patrickleboutillier/flash6502/docs/kicad/flash6502/ALU.kicad_sch

## KiCad design docs/kicad/flash6502/ALU.kicad_sch (2023-03-12, an earlier design)

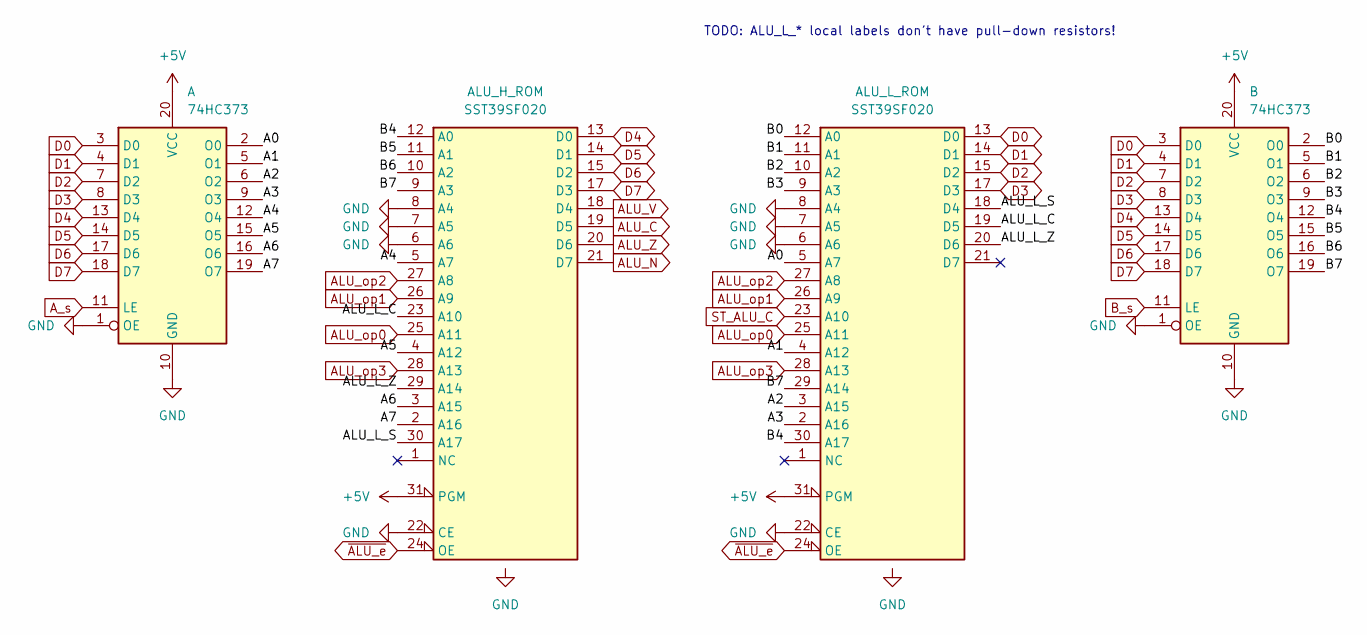
[picture p24: schematic ALU.kicad_sch]

Parts:
A: 74HC373
ALU_H_ROM: SST39SF020
ALU_L_ROM: SST39SF020
B: 74HC373

Connections:
+5V: A.20 (VCC), ALU_H_ROM.31 (PGM), ALU_L_ROM.31 (PGM), B.20 (VCC)
A0: A.2 (O0), ALU_L_ROM.5 (A7)
A1: A.5 (O1), ALU_L_ROM.4 (A12)
A2: A.6 (O2), ALU_L_ROM.3 (A15)
A3: A.9 (O3), ALU_L_ROM.2 (A16)
A4: A.12 (O4), ALU_H_ROM.5 (A7)
A5: A.15 (O5), ALU_H_ROM.4 (A12)
A6: A.16 (O6), ALU_H_ROM.3 (A15)
A7: A.19 (O7), ALU_H_ROM.2 (A16)
ALU_C: ALU_H_ROM.19 (D5)
ALU_L_C: ALU_H_ROM.23 (A10), ALU_L_ROM.19 (D5)
ALU_L_S: ALU_H_ROM.30 (A17), ALU_L_ROM.18 (D4)
ALU_L_Z: ALU_H_ROM.29 (A14), ALU_L_ROM.20 (D6)
ALU_N: ALU_H_ROM.21 (D7)
ALU_V: ALU_H_ROM.18 (D4)
ALU_Z: ALU_H_ROM.20 (D6)
ALU_op0: ALU_H_ROM.25 (A11), ALU_L_ROM.25 (A11)
ALU_op1: ALU_H_ROM.26 (A9), ALU_L_ROM.26 (A9)
ALU_op2: ALU_H_ROM.27 (A8), ALU_L_ROM.27 (A8)
ALU_op3: ALU_H_ROM.28 (A13), ALU_L_ROM.28 (A13)
A_s: A.11 (LE)
B0: ALU_L_ROM.12 (A0), B.2 (O0)
B1: ALU_L_ROM.11 (A1), B.5 (O1)
B2: ALU_L_ROM.10 (A2), B.6 (O2)
B3: ALU_L_ROM.9 (A3), B.9 (O3)
B4: ALU_H_ROM.12 (A0), ALU_L_ROM.30 (A17), B.12 (O4)
B5: ALU_H_ROM.11 (A1), B.15 (O5)
B6: ALU_H_ROM.10 (A2), B.16 (O6)
B7: ALU_H_ROM.9 (A3), ALU_L_ROM.29 (A14), B.19 (O7)
B_s: B.11 (LE)
D0: A.3 (D0), ALU_L_ROM.13 (D0), B.3 (D0)
D1: A.4 (D1), ALU_L_ROM.14 (D1), B.4 (D1)
D2: A.7 (D2), ALU_L_ROM.15 (D2), B.7 (D2)
D3: A.8 (D3), ALU_L_ROM.17 (D3), B.8 (D3)
D4: A.13 (D4), ALU_H_ROM.13 (D0), B.13 (D4)
D5: A.14 (D5), ALU_H_ROM.14 (D1), B.14 (D5)
D6: A.17 (D6), ALU_H_ROM.15 (D2), B.17 (D6)
D7: A.18 (D7), ALU_H_ROM.17 (D3), B.18 (D7)
GND: A.1 (OE), A.10 (GND), ALU_H_ROM.6 (A6), ALU_H_ROM.7 (A5), ALU_H_ROM.8 (A4), ALU_H_ROM.16 (GND), ALU_H_ROM.22 (CE), ALU_L_ROM.6 (A6), ALU_L_ROM.7 (A5), ALU_L_ROM.8 (A4), ALU_L_ROM.16 (GND), ALU_L_ROM.22 (CE), B.1 (OE), B.10 (GND)
ST_ALU_C: ALU_L_ROM.23 (A10)
~ALU_e: ALU_H_ROM.24 (OE), ALU_L_ROM.24 (OE)

Notes on the sheet:
TODO: ALU_L_* local labels don't have pull-down resistors!
