patrickleboutillier/flash6502/docs/kicad/flash6502/Address_High.kicad_sch

## KiCad design docs/kicad/flash6502/Address_High.kicad_sch (2023-03-12, an earlier design)

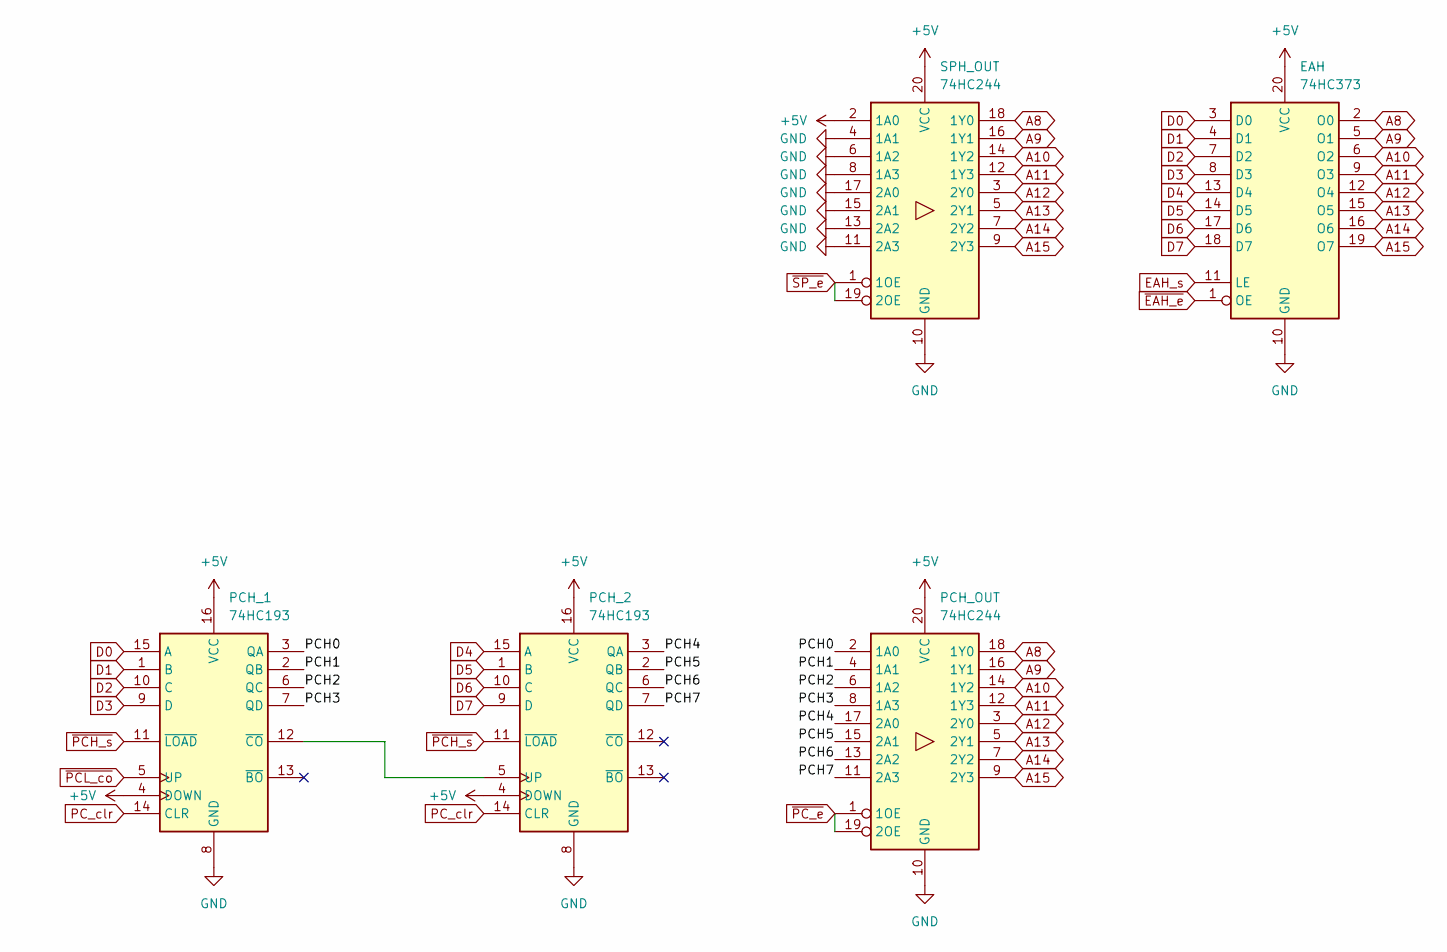
[picture p25: schematic Address_High.kicad_sch]

Parts:
EAH: 74HC373
PCH_1, PCH_2: 74HC193
PCH_OUT: 74HC244
SPH_OUT: 74HC244

Connections:
+5V: EAH.20 (VCC), PCH_1.4 (DOWN), PCH_1.16 (VCC), PCH_2.4 (DOWN), PCH_2.16 (VCC), PCH_OUT.20 (VCC), SPH_OUT.2 (1A0), SPH_OUT.20 (VCC)
A8: EAH.2 (O0), PCH_OUT.18 (1Y0), SPH_OUT.18 (1Y0)
A9: EAH.5 (O1), PCH_OUT.16 (1Y1), SPH_OUT.16 (1Y1)
A10: EAH.6 (O2), PCH_OUT.14 (1Y2), SPH_OUT.14 (1Y2)
A11: EAH.9 (O3), PCH_OUT.12 (1Y3), SPH_OUT.12 (1Y3)
A12: EAH.12 (O4), PCH_OUT.3 (2Y0), SPH_OUT.3 (2Y0)
A13: EAH.15 (O5), PCH_OUT.5 (2Y1), SPH_OUT.5 (2Y1)
A14: EAH.16 (O6), PCH_OUT.7 (2Y2), SPH_OUT.7 (2Y2)
A15: EAH.19 (O7), PCH_OUT.9 (2Y3), SPH_OUT.9 (2Y3)
D0: EAH.3 (D0), PCH_1.15 (A)
D1: EAH.4 (D1), PCH_1.1 (B)
D2: EAH.7 (D2), PCH_1.10 (C)
D3: EAH.8 (D3), PCH_1.9 (D)
D4: EAH.13 (D4), PCH_2.15 (A)
D5: EAH.14 (D5), PCH_2.1 (B)
D6: EAH.17 (D6), PCH_2.10 (C)
D7: EAH.18 (D7), PCH_2.9 (D)
EAH_s: EAH.11 (LE)
GND: EAH.10 (GND), PCH_1.8 (GND), PCH_2.8 (GND), PCH_OUT.10 (GND), SPH_OUT.4 (1A1), SPH_OUT.6 (1A2), SPH_OUT.8 (1A3), SPH_OUT.10 (GND), SPH_OUT.11 (2A3), SPH_OUT.13 (2A2), SPH_OUT.15 (2A1), SPH_OUT.17 (2A0)
unnamed: PCH_1.12 (~CO), PCH_2.5 (UP)
PCH0: PCH_1.3 (QA), PCH_OUT.2 (1A0)
PCH1: PCH_1.2 (QB), PCH_OUT.4 (1A1)
PCH2: PCH_1.6 (QC), PCH_OUT.6 (1A2)
PCH3: PCH_1.7 (QD), PCH_OUT.8 (1A3)
PCH4: PCH_2.3 (QA), PCH_OUT.17 (2A0)
PCH5: PCH_2.2 (QB), PCH_OUT.15 (2A1)
PCH6: PCH_2.6 (QC), PCH_OUT.13 (2A2)
PCH7: PCH_2.7 (QD), PCH_OUT.11 (2A3)
PC_clr: PCH_1.14 (CLR), PCH_2.14 (CLR)
~EAH_e: EAH.1 (OE)
~PCH_s: PCH_1.11 (~LOAD), PCH_2.11 (~LOAD)
~PCL_co: PCH_1.5 (UP)
~PC_e: PCH_OUT.1 (1OE), PCH_OUT.19 (2OE)
~SP_e: SPH_OUT.1 (1OE), SPH_OUT.19 (2OE)
