patrickleboutillier/flash6502/docs/kicad/flash6502/Address_Low.kicad_sch

## KiCad design docs/kicad/flash6502/Address_Low.kicad_sch (2023-03-12, an earlier design)

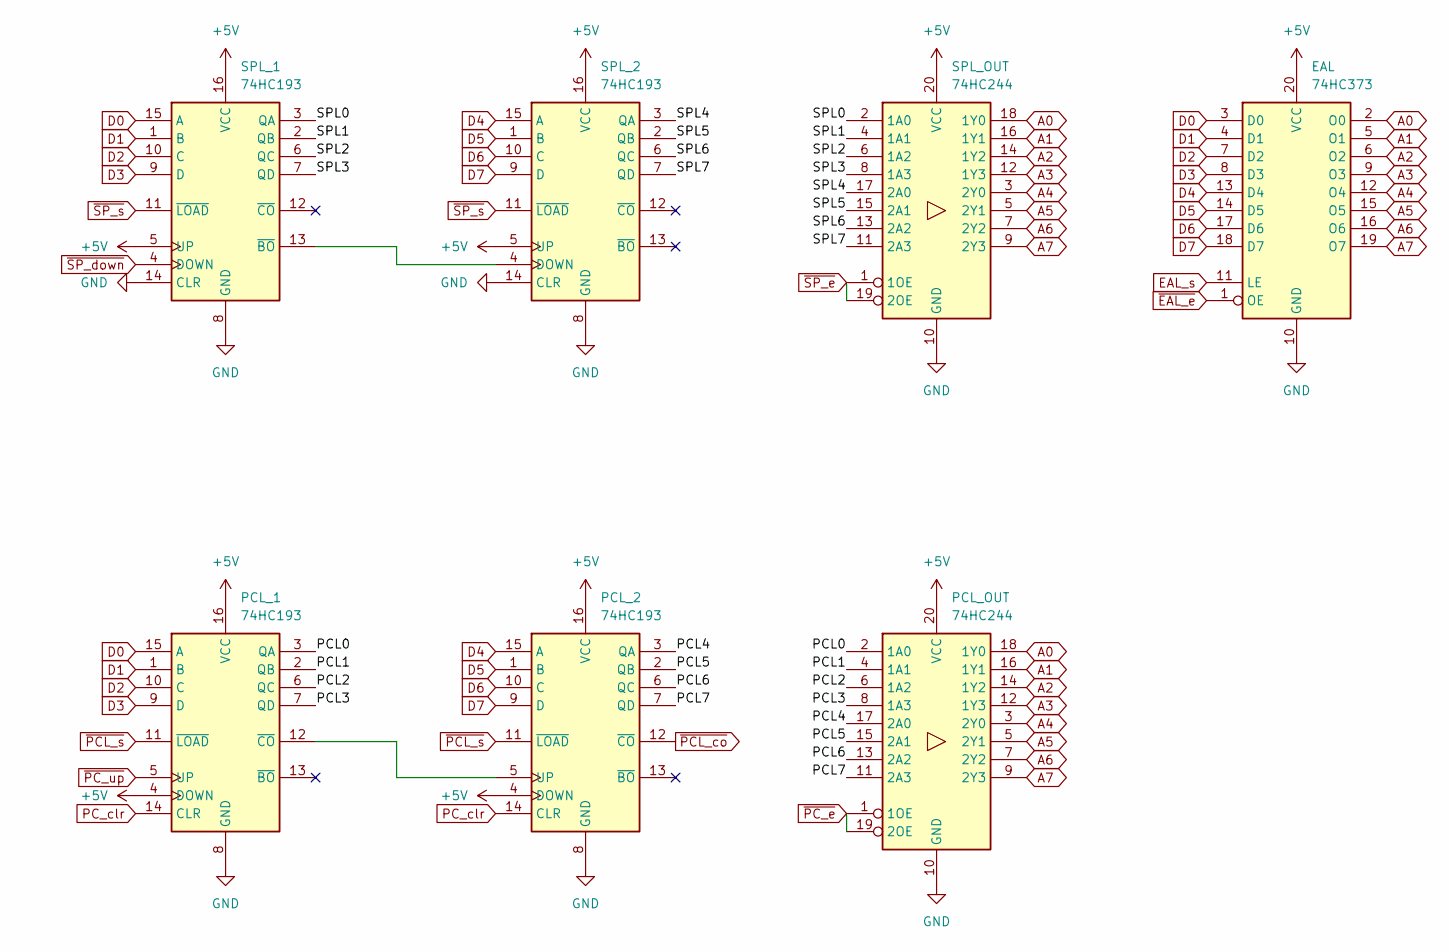
[picture p26: schematic Address_Low.kicad_sch]

Parts:
EAL: 74HC373
PCL_1, PCL_2: 74HC193
PCL_OUT: 74HC244
SPL_1, SPL_2: 74HC193
SPL_OUT: 74HC244

Connections:
+5V: EAL.20 (VCC), PCL_1.4 (DOWN), PCL_1.16 (VCC), PCL_2.4 (DOWN), PCL_2.16 (VCC), PCL_OUT.20 (VCC), SPL_1.5 (UP), SPL_1.16 (VCC), SPL_2.5 (UP), SPL_2.16 (VCC), SPL_OUT.20 (VCC)
A0: EAL.2 (O0), PCL_OUT.18 (1Y0), SPL_OUT.18 (1Y0)
A1: EAL.5 (O1), PCL_OUT.16 (1Y1), SPL_OUT.16 (1Y1)
A2: EAL.6 (O2), PCL_OUT.14 (1Y2), SPL_OUT.14 (1Y2)
A3: EAL.9 (O3), PCL_OUT.12 (1Y3), SPL_OUT.12 (1Y3)
A4: EAL.12 (O4), PCL_OUT.3 (2Y0), SPL_OUT.3 (2Y0)
A5: EAL.15 (O5), PCL_OUT.5 (2Y1), SPL_OUT.5 (2Y1)
A6: EAL.16 (O6), PCL_OUT.7 (2Y2), SPL_OUT.7 (2Y2)
A7: EAL.19 (O7), PCL_OUT.9 (2Y3), SPL_OUT.9 (2Y3)
D0: EAL.3 (D0), PCL_1.15 (A), SPL_1.15 (A)
D1: EAL.4 (D1), PCL_1.1 (B), SPL_1.1 (B)
D2: EAL.7 (D2), PCL_1.10 (C), SPL_1.10 (C)
D3: EAL.8 (D3), PCL_1.9 (D), SPL_1.9 (D)
D4: EAL.13 (D4), PCL_2.15 (A), SPL_2.15 (A)
D5: EAL.14 (D5), PCL_2.1 (B), SPL_2.1 (B)
D6: EAL.17 (D6), PCL_2.10 (C), SPL_2.10 (C)
D7: EAL.18 (D7), PCL_2.9 (D), SPL_2.9 (D)
EAL_s: EAL.11 (LE)
GND: EAL.10 (GND), PCL_1.8 (GND), PCL_2.8 (GND), PCL_OUT.10 (GND), SPL_1.8 (GND), SPL_1.14 (CLR), SPL_2.8 (GND), SPL_2.14 (CLR), SPL_OUT.10 (GND)
unnamed: PCL_1.12 (~CO), PCL_2.5 (UP)
unnamed: SPL_1.13 (~BO), SPL_2.4 (DOWN)
PCL0: PCL_1.3 (QA), PCL_OUT.2 (1A0)
PCL1: PCL_1.2 (QB), PCL_OUT.4 (1A1)
PCL2: PCL_1.6 (QC), PCL_OUT.6 (1A2)
PCL3: PCL_1.7 (QD), PCL_OUT.8 (1A3)
PCL4: PCL_2.3 (QA), PCL_OUT.17 (2A0)
PCL5: PCL_2.2 (QB), PCL_OUT.15 (2A1)
PCL6: PCL_2.6 (QC), PCL_OUT.13 (2A2)
PCL7: PCL_2.7 (QD), PCL_OUT.11 (2A3)
PC_clr: PCL_1.14 (CLR), PCL_2.14 (CLR)
SPL0: SPL_1.3 (QA), SPL_OUT.2 (1A0)
SPL1: SPL_1.2 (QB), SPL_OUT.4 (1A1)
SPL2: SPL_1.6 (QC), SPL_OUT.6 (1A2)
SPL3: SPL_1.7 (QD), SPL_OUT.8 (1A3)
SPL4: SPL_2.3 (QA), SPL_OUT.17 (2A0)
SPL5: SPL_2.2 (QB), SPL_OUT.15 (2A1)
SPL6: SPL_2.6 (QC), SPL_OUT.13 (2A2)
SPL7: SPL_2.7 (QD), SPL_OUT.11 (2A3)
~EAL_e: EAL.1 (OE)
~PCL_co: PCL_2.12 (~CO)
~PCL_s: PCL_1.11 (~LOAD), PCL_2.11 (~LOAD)
~PC_e: PCL_OUT.1 (1OE), PCL_OUT.19 (2OE)
~PC_up: PCL_1.5 (UP)
~SP_down: SPL_1.4 (DOWN)
~SP_e: SPL_OUT.1 (1OE), SPL_OUT.19 (2OE)
~SP_s: SPL_1.11 (~LOAD), SPL_2.11 (~LOAD)
