patrickleboutillier/flash6502/docs/kicad/flash6502/CTRL3.kicad_sch

## KiCad design docs/kicad/flash6502/CTRL3.kicad_sch (2023-02-26, an earlier design)

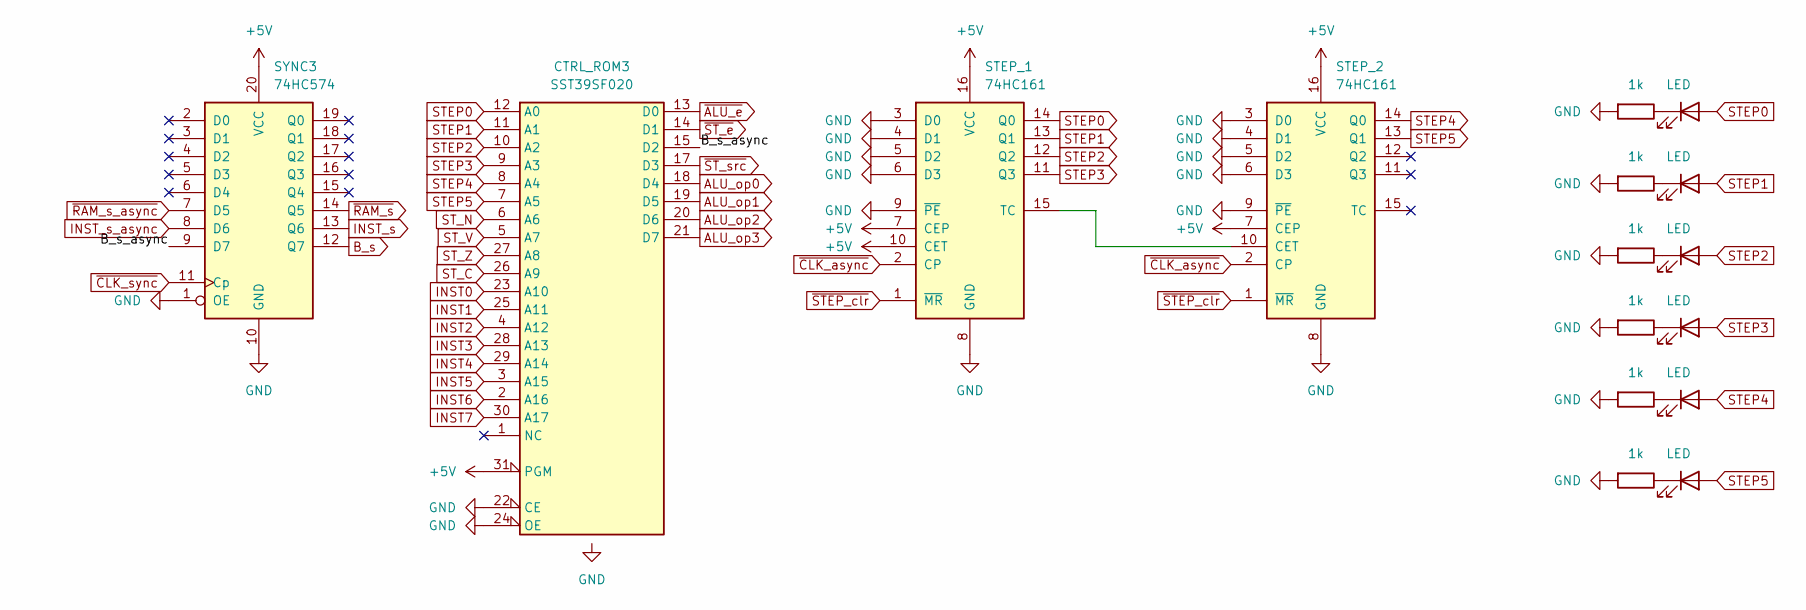
[picture p27: schematic CTRL3.kicad_sch]

Parts:
CTRL_ROM3: SST39SF020
LEDSTEP0, LEDSTEP1, LEDSTEP2, LEDSTEP3, LEDSTEP4, LEDSTEP5: LED
RSTEP0, RSTEP1, RSTEP2, RSTEP3, RSTEP4, RSTEP5: 1k
STEP_1, STEP_2: 74HC161
SYNC3: 74HC574

Connections:
+5V: CTRL_ROM3.31 (PGM), STEP_1.7 (CEP), STEP_1.10 (CET), STEP_1.16 (VCC), STEP_2.7 (CEP), STEP_2.16 (VCC), SYNC3.20 (VCC)
ALU_op0: CTRL_ROM3.18 (D4)
ALU_op1: CTRL_ROM3.19 (D5)
ALU_op2: CTRL_ROM3.20 (D6)
ALU_op3: CTRL_ROM3.21 (D7)
B_s: SYNC3.12 (Q7)
B_s_async: CTRL_ROM3.15 (D2), SYNC3.9 (D7)
GND: CTRL_ROM3.16 (GND), CTRL_ROM3.22 (CE), CTRL_ROM3.24 (OE), RSTEP0.2, RSTEP1.2, RSTEP2.2, RSTEP3.2, RSTEP4.2, RSTEP5.2, STEP_1.3 (D0), STEP_1.4 (D1), STEP_1.5 (D2), STEP_1.6 (D3), STEP_1.8 (GND), STEP_1.9 (~PE), STEP_2.3 (D0), STEP_2.4 (D1), STEP_2.5 (D2), STEP_2.6 (D3), STEP_2.8 (GND), STEP_2.9 (~PE), SYNC3.1 (OE), SYNC3.10 (GND)
INST0: CTRL_ROM3.23 (A10)
INST1: CTRL_ROM3.25 (A11)
INST2: CTRL_ROM3.4 (A12)
INST3: CTRL_ROM3.28 (A13)
INST4: CTRL_ROM3.29 (A14)
INST5: CTRL_ROM3.3 (A15)
INST6: CTRL_ROM3.2 (A16)
INST7: CTRL_ROM3.30 (A17)
INST_s: SYNC3.13 (Q6)
INST_s_async: SYNC3.8 (D6)
unnamed: LEDSTEP0.1 (K), RSTEP0.1
unnamed: LEDSTEP1.1 (K), RSTEP1.1
unnamed: LEDSTEP2.1 (K), RSTEP2.1
unnamed: LEDSTEP3.1 (K), RSTEP3.1
unnamed: LEDSTEP4.1 (K), RSTEP4.1
unnamed: LEDSTEP5.1 (K), RSTEP5.1
unnamed: STEP_1.15 (TC), STEP_2.10 (CET)
STEP0: CTRL_ROM3.12 (A0), LEDSTEP0.2 (A), STEP_1.14 (Q0)
STEP1: CTRL_ROM3.11 (A1), LEDSTEP1.2 (A), STEP_1.13 (Q1)
STEP2: CTRL_ROM3.10 (A2), LEDSTEP2.2 (A), STEP_1.12 (Q2)
STEP3: CTRL_ROM3.9 (A3), LEDSTEP3.2 (A), STEP_1.11 (Q3)
STEP4: CTRL_ROM3.8 (A4), LEDSTEP4.2 (A), STEP_2.14 (Q0)
STEP5: CTRL_ROM3.7 (A5), LEDSTEP5.2 (A), STEP_2.13 (Q1)
ST_C: CTRL_ROM3.26 (A9)
ST_N: CTRL_ROM3.6 (A6)
ST_V: CTRL_ROM3.5 (A7)
ST_Z: CTRL_ROM3.27 (A8)
~ALU_e: CTRL_ROM3.13 (D0)
~CLK_async: STEP_1.2 (CP), STEP_2.2 (CP)
~CLK_sync: SYNC3.11 (Cp)
~RAM_s_async: SYNC3.7 (D5)
~RAM_s: SYNC3.14 (Q5)
~STEP_clr: STEP_1.1 (~MR), STEP_2.1 (~MR)
~ST_e: CTRL_ROM3.14 (D1)
~ST_src: CTRL_ROM3.17 (D3)
