patrickleboutillier/flash6502/docs/kicad/flash6502/CTRL12.kicad_sch

## KiCad design docs/kicad/flash6502/CTRL12.kicad_sch (2023-02-26, an earlier design)

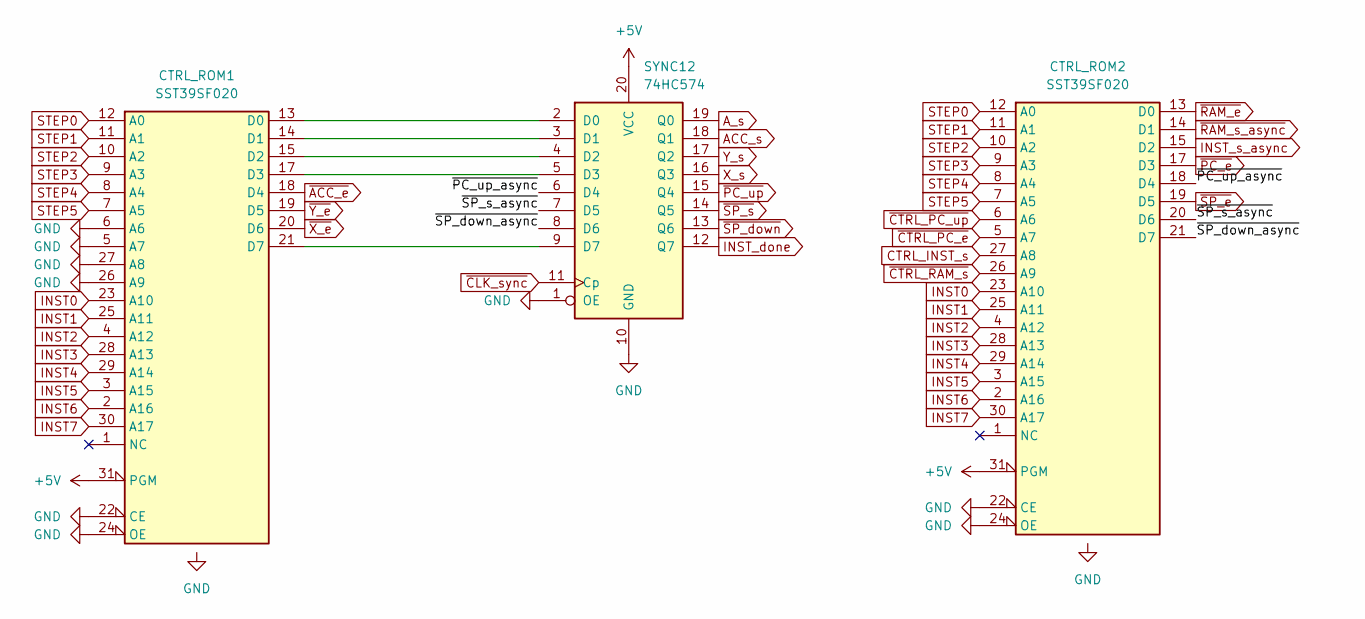
[picture p28: schematic CTRL12.kicad_sch]

Parts:
CTRL_ROM1, CTRL_ROM2: SST39SF020
SYNC12: 74HC574

Connections:
+5V: CTRL_ROM1.31 (PGM), CTRL_ROM2.31 (PGM), SYNC12.20 (VCC)
ACC_s: SYNC12.18 (Q1)
A_s: SYNC12.19 (Q0)
CTRL_INST_s: CTRL_ROM2.27 (A8)
GND: CTRL_ROM1.5 (A7), CTRL_ROM1.6 (A6), CTRL_ROM1.16 (GND), CTRL_ROM1.22 (CE), CTRL_ROM1.24 (OE), CTRL_ROM1.26 (A9), CTRL_ROM1.27 (A8), CTRL_ROM2.16 (GND), CTRL_ROM2.22 (CE), CTRL_ROM2.24 (OE), SYNC12.1 (OE), SYNC12.10 (GND)
INST0: CTRL_ROM1.23 (A10), CTRL_ROM2.23 (A10)
INST1: CTRL_ROM1.25 (A11), CTRL_ROM2.25 (A11)
INST2: CTRL_ROM1.4 (A12), CTRL_ROM2.4 (A12)
INST3: CTRL_ROM1.28 (A13), CTRL_ROM2.28 (A13)
INST4: CTRL_ROM1.29 (A14), CTRL_ROM2.29 (A14)
INST5: CTRL_ROM1.3 (A15), CTRL_ROM2.3 (A15)
INST6: CTRL_ROM1.2 (A16), CTRL_ROM2.2 (A16)
INST7: CTRL_ROM1.30 (A17), CTRL_ROM2.30 (A17)
INST_done: SYNC12.12 (Q7)
INST_s_async: CTRL_ROM2.15 (D2)
unnamed: CTRL_ROM1.13 (D0), SYNC12.2 (D0)
unnamed: CTRL_ROM1.14 (D1), SYNC12.3 (D1)
unnamed: CTRL_ROM1.15 (D2), SYNC12.4 (D2)
unnamed: CTRL_ROM1.17 (D3), SYNC12.5 (D3)
unnamed: CTRL_ROM1.21 (D7), SYNC12.9 (D7)
STEP0: CTRL_ROM1.12 (A0), CTRL_ROM2.12 (A0)
STEP1: CTRL_ROM1.11 (A1), CTRL_ROM2.11 (A1)
STEP2: CTRL_ROM1.10 (A2), CTRL_ROM2.10 (A2)
STEP3: CTRL_ROM1.9 (A3), CTRL_ROM2.9 (A3)
STEP4: CTRL_ROM1.8 (A4), CTRL_ROM2.8 (A4)
STEP5: CTRL_ROM1.7 (A5), CTRL_ROM2.7 (A5)
X_s: SYNC12.16 (Q3)
Y_s: SYNC12.17 (Q2)
~ACC_e: CTRL_ROM1.18 (D4)
~CLK_sync: SYNC12.11 (Cp)
~CTRL_PC_e: CTRL_ROM2.5 (A7)
~CTRL_PC_up: CTRL_ROM2.6 (A6)
~CTRL_RAM_s: CTRL_ROM2.26 (A9)
~PC_e: CTRL_ROM2.17 (D3)
~PC_up_async: CTRL_ROM2.18 (D4), SYNC12.6 (D4)
~PC_up: SYNC12.15 (Q4)
~RAM_e: CTRL_ROM2.13 (D0)
~RAM_s_async: CTRL_ROM2.14 (D1)
~SP_down_async: CTRL_ROM2.21 (D7), SYNC12.8 (D6)
~SP_down: SYNC12.13 (Q6)
~SP_e: CTRL_ROM2.19 (D5)
~SP_s_async: CTRL_ROM2.20 (D6), SYNC12.7 (D5)
~SP_s: SYNC12.14 (Q5)
~X_e: CTRL_ROM1.20 (D6)
~Y_e: CTRL_ROM1.19 (D5)
