patrickleboutillier/flash6502/docs/kicad/flash6502/CTRL45.kicad_sch

## KiCad design docs/kicad/flash6502/CTRL45.kicad_sch (2023-02-26, an earlier design)

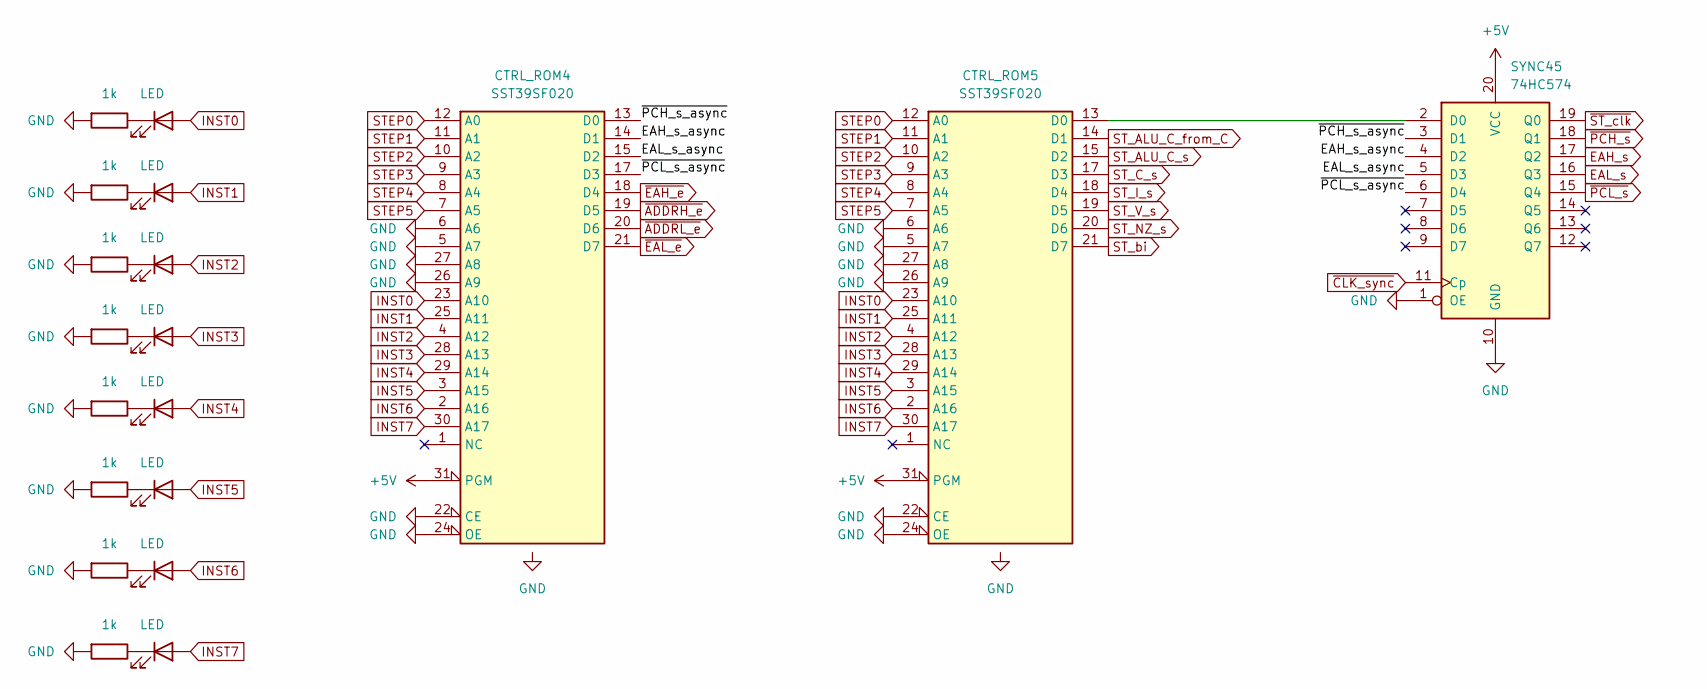
[picture p29: schematic CTRL45.kicad_sch]

Parts:
CTRL_ROM4, CTRL_ROM5: SST39SF020
LEDI0, LEDI1, LEDI2, LEDI3, LEDI4, LEDI5, LEDI6, LEDI7: LED
RLI0, RLI1, RLI2, RLI3, RLI4, RLI5, RLI6, RLI7: 1k
SYNC45: 74HC574

Connections:
+5V: CTRL_ROM4.31 (PGM), CTRL_ROM5.31 (PGM), SYNC45.20 (VCC)
EAH_s: SYNC45.17 (Q2)
EAH_s_async: CTRL_ROM4.14 (D1), SYNC45.4 (D2)
EAL_s: SYNC45.16 (Q3)
EAL_s_async: CTRL_ROM4.15 (D2), SYNC45.5 (D3)
GND: CTRL_ROM4.5 (A7), CTRL_ROM4.6 (A6), CTRL_ROM4.16 (GND), CTRL_ROM4.22 (CE), CTRL_ROM4.24 (OE), CTRL_ROM4.26 (A9), CTRL_ROM4.27 (A8), CTRL_ROM5.5 (A7), CTRL_ROM5.6 (A6), CTRL_ROM5.16 (GND), CTRL_ROM5.22 (CE), CTRL_ROM5.24 (OE), CTRL_ROM5.26 (A9), CTRL_ROM5.27 (A8), SYNC45.1 (OE), SYNC45.10 (GND)
INST0: CTRL_ROM4.23 (A10), CTRL_ROM5.23 (A10), LEDI0.2 (A)
INST1: CTRL_ROM4.25 (A11), CTRL_ROM5.25 (A11), LEDI1.2 (A)
INST2: CTRL_ROM4.4 (A12), CTRL_ROM5.4 (A12), LEDI2.2 (A)
INST3: CTRL_ROM4.28 (A13), CTRL_ROM5.28 (A13), LEDI3.2 (A)
INST4: CTRL_ROM4.29 (A14), CTRL_ROM5.29 (A14), LEDI4.2 (A)
INST5: CTRL_ROM4.3 (A15), CTRL_ROM5.3 (A15), LEDI5.2 (A)
INST6: CTRL_ROM4.2 (A16), CTRL_ROM5.2 (A16), LEDI6.2 (A)
INST7: CTRL_ROM4.30 (A17), CTRL_ROM5.30 (A17), LEDI7.2 (A)
unnamed: CTRL_ROM5.13 (D0), SYNC45.2 (D0)
unnamed: LEDI0.1 (K), RLI0.1
unnamed: LEDI1.1 (K), RLI1.1
unnamed: LEDI2.1 (K), RLI2.1
unnamed: LEDI3.1 (K), RLI3.1
unnamed: LEDI4.1 (K), RLI4.1
unnamed: LEDI5.1 (K), RLI5.1
unnamed: LEDI6.1 (K), RLI6.1
unnamed: LEDI7.1 (K), RLI7.1
STEP0: CTRL_ROM4.12 (A0), CTRL_ROM5.12 (A0)
STEP1: CTRL_ROM4.11 (A1), CTRL_ROM5.11 (A1)
STEP2: CTRL_ROM4.10 (A2), CTRL_ROM5.10 (A2)
STEP3: CTRL_ROM4.9 (A3), CTRL_ROM5.9 (A3)
STEP4: CTRL_ROM4.8 (A4), CTRL_ROM5.8 (A4)
STEP5: CTRL_ROM4.7 (A5), CTRL_ROM5.7 (A5)
ST_ALU_C_from_C: CTRL_ROM5.14 (D1)
ST_ALU_C_s: CTRL_ROM5.15 (D2)
ST_C_s: CTRL_ROM5.17 (D3)
ST_I_s: CTRL_ROM5.18 (D4)
ST_NZ_s: CTRL_ROM5.20 (D6)
ST_V_s: CTRL_ROM5.19 (D5)
ST_bi: CTRL_ROM5.21 (D7)
~ADDRH_e: CTRL_ROM4.19 (D5)
~ADDRL_e: CTRL_ROM4.20 (D6)
~CLK_sync: SYNC45.11 (Cp)
~EAH_e: CTRL_ROM4.18 (D4)
~EAL_e: CTRL_ROM4.21 (D7)
~PCH_s_async: CTRL_ROM4.13 (D0), SYNC45.3 (D1)
~PCH_s: SYNC45.18 (Q1)
~PCL_s_async: CTRL_ROM4.17 (D3), SYNC45.6 (D4)
~PCL_s: SYNC45.15 (Q4)
~ST_clk: SYNC45.19 (Q0)
