patrickleboutillier/flash6502/docs/kicad/flash6502/Controller.kicad_sch

## KiCad design docs/kicad/flash6502/Controller.kicad_sch (2023-03-12, an earlier design)

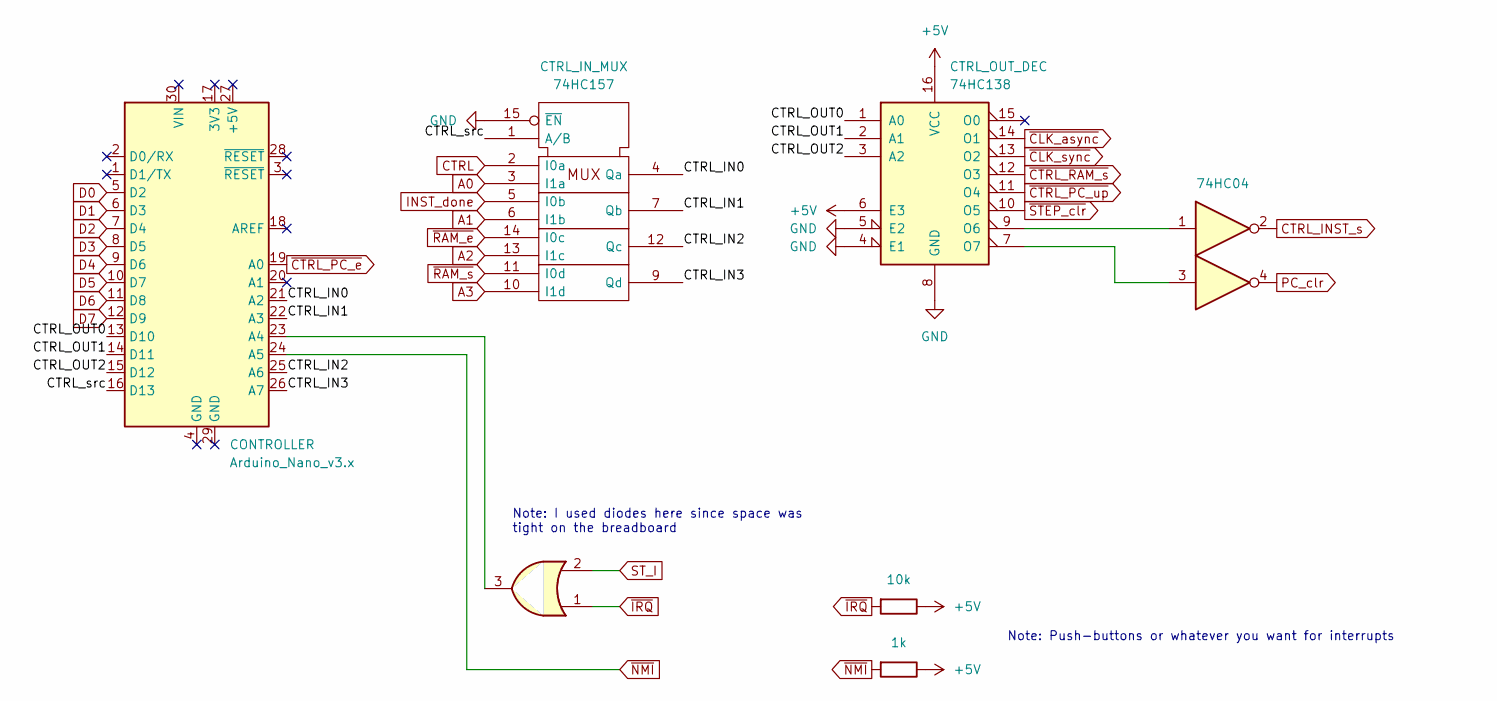
[picture p30: schematic Controller.kicad_sch]

Parts:
CONTROLLER: Arduino_Nano_v3.x; Arduino_Nano
CTRL_INST_s_NOT: 74HC04
CTRL_IN_MUX: 74HC157
CTRL_OUT_DEC: 74HC138
IRQ_OR: 74HC32
PC_clr_NOT: 74HC04
RIRQ: 10k
RNMI: 1k

Connections:
+5V: CTRL_OUT_DEC.6 (E3), CTRL_OUT_DEC.16 (VCC), RIRQ.1, RNMI.1
A0: CTRL_IN_MUX.3 (I1a)
A1: CTRL_IN_MUX.6 (I1b)
A2: CTRL_IN_MUX.13 (I1c)
A3: CTRL_IN_MUX.10 (I1d)
CTRL: CTRL_IN_MUX.2 (I0a)
CTRL_IN0: CONTROLLER.21 (A2), CTRL_IN_MUX.4 (Qa)
CTRL_IN1: CONTROLLER.22 (A3), CTRL_IN_MUX.7 (Qb)
CTRL_IN2: CONTROLLER.25 (A6), CTRL_IN_MUX.12 (Qc)
CTRL_IN3: CONTROLLER.26 (A7), CTRL_IN_MUX.9 (Qd)
CTRL_INST_s: CTRL_INST_s_NOT.2
CTRL_OUT0: CONTROLLER.13 (D10), CTRL_OUT_DEC.1 (A0)
CTRL_OUT1: CONTROLLER.14 (D11), CTRL_OUT_DEC.2 (A1)
CTRL_OUT2: CONTROLLER.15 (D12), CTRL_OUT_DEC.3 (A2)
CTRL_src: CONTROLLER.16 (D13), CTRL_IN_MUX.1 (A/B)
D0: CONTROLLER.5 (D2)
D1: CONTROLLER.6 (D3)
D2: CONTROLLER.7 (D4)
D3: CONTROLLER.8 (D5)
D4: CONTROLLER.9 (D6)
D5: CONTROLLER.10 (D7)
D6: CONTROLLER.11 (D8)
D7: CONTROLLER.12 (D9)
GND: CTRL_IN_MUX.15 (~EN), CTRL_OUT_DEC.4 (E1), CTRL_OUT_DEC.5 (E2), CTRL_OUT_DEC.8 (GND)
INST_done: CTRL_IN_MUX.5 (I0b)
unnamed: CONTROLLER.23 (A4), IRQ_OR.3
unnamed: CTRL_INST_s_NOT.1, CTRL_OUT_DEC.9 (O6)
unnamed: CTRL_OUT_DEC.7 (O7), PC_clr_NOT.3
PC_clr: PC_clr_NOT.4
ST_I: IRQ_OR.2
~CLK_async: CTRL_OUT_DEC.14 (O1)
~CLK_sync: CTRL_OUT_DEC.13 (O2)
~CTRL_PC_e: CONTROLLER.19 (A0)
~CTRL_PC_up: CTRL_OUT_DEC.11 (O4)
~CTRL_RAM_s: CTRL_OUT_DEC.12 (O3)
~IRQ: IRQ_OR.1, RIRQ.2
~NMI: CONTROLLER.24 (A5), RNMI.2
~RAM_e: CTRL_IN_MUX.14 (I0c)
~RAM_s: CTRL_IN_MUX.11 (I0d)
~STEP_clr: CTRL_OUT_DEC.10 (O5)

Notes on the sheet:
Note: I used diodes here since space was tight on the breadboard
Note: Push-buttons or whatever you want for interrupts
