patrickleboutillier/flash6502/docs/kicad/flash6502/RAM.kicad_sch

## KiCad design docs/kicad/flash6502/RAM.kicad_sch (2023-03-12, an earlier design)

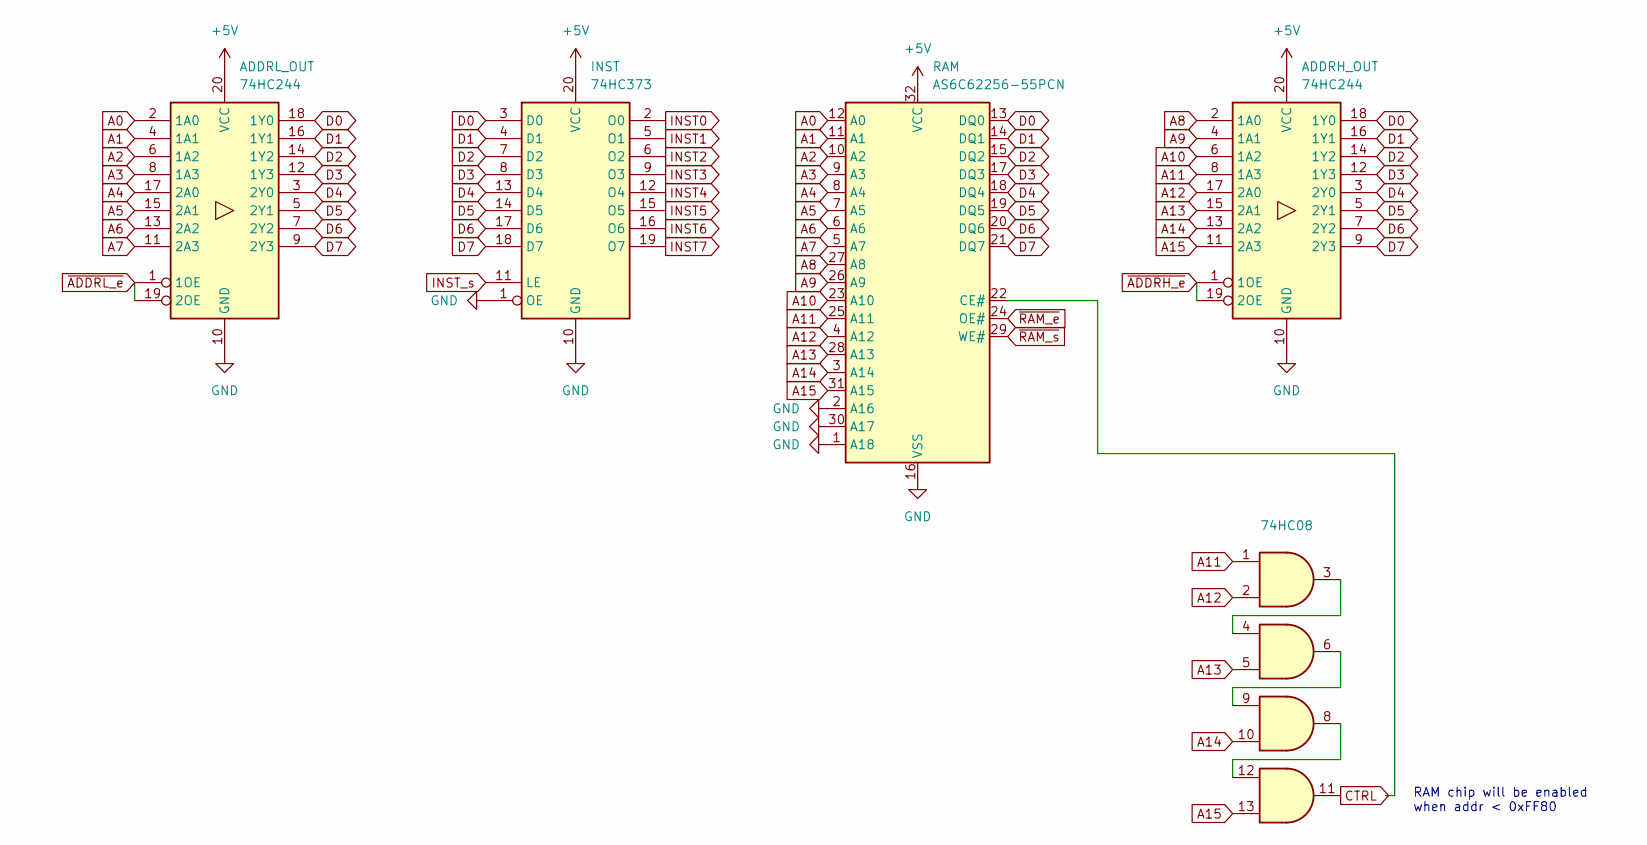
[picture p31: schematic RAM.kicad_sch]

Parts:
ADDRH_OUT: 74HC244
ADDRL_OUT: 74HC244
CTRL: 7408
CTRL_AND: 74HC08
INST: 74HC373
RAM: AS6C62256-55PCN; DIP-32_W15.24mm

Connections:
+5V: ADDRH_OUT.20 (VCC), ADDRL_OUT.20 (VCC), INST.20 (VCC), RAM.32 (VCC)
A0: ADDRL_OUT.2 (1A0), RAM.12 (A0)
A1: ADDRL_OUT.4 (1A1), RAM.11 (A1)
A2: ADDRL_OUT.6 (1A2), RAM.10 (A2)
A3: ADDRL_OUT.8 (1A3), RAM.9 (A3)
A4: ADDRL_OUT.17 (2A0), RAM.8 (A4)
A5: ADDRL_OUT.15 (2A1), RAM.7 (A5)
A6: ADDRL_OUT.13 (2A2), RAM.6 (A6)
A7: ADDRL_OUT.11 (2A3), RAM.5 (A7)
A8: ADDRH_OUT.2 (1A0), RAM.27 (A8)
A9: ADDRH_OUT.4 (1A1), RAM.26 (A9)
A10: ADDRH_OUT.6 (1A2), RAM.23 (A10)
A11: ADDRH_OUT.8 (1A3), CTRL_AND.1, RAM.25 (A11)
A12: ADDRH_OUT.17 (2A0), CTRL_AND.2, RAM.4 (A12)
A13: ADDRH_OUT.15 (2A1), CTRL.5, RAM.28 (A13)
A14: ADDRH_OUT.13 (2A2), CTRL.10, RAM.3 (A14)
A15: ADDRH_OUT.11 (2A3), CTRL.13, RAM.31 (A15)
CTRL: CTRL.11
D0: ADDRH_OUT.18 (1Y0), ADDRL_OUT.18 (1Y0), INST.3 (D0), RAM.13 (DQ0)
D1: ADDRH_OUT.16 (1Y1), ADDRL_OUT.16 (1Y1), INST.4 (D1), RAM.14 (DQ1)
D2: ADDRH_OUT.14 (1Y2), ADDRL_OUT.14 (1Y2), INST.7 (D2), RAM.15 (DQ2)
D3: ADDRH_OUT.12 (1Y3), ADDRL_OUT.12 (1Y3), INST.8 (D3), RAM.17 (DQ3)
D4: ADDRH_OUT.3 (2Y0), ADDRL_OUT.3 (2Y0), INST.13 (D4), RAM.18 (DQ4)
D5: ADDRH_OUT.5 (2Y1), ADDRL_OUT.5 (2Y1), INST.14 (D5), RAM.19 (DQ5)
D6: ADDRH_OUT.7 (2Y2), ADDRL_OUT.7 (2Y2), INST.17 (D6), RAM.20 (DQ6)
D7: ADDRH_OUT.9 (2Y3), ADDRL_OUT.9 (2Y3), INST.18 (D7), RAM.21 (DQ7)
GND: ADDRH_OUT.10 (GND), ADDRL_OUT.10 (GND), INST.1 (OE), INST.10 (GND), RAM.1 (A18), RAM.2 (A16), RAM.16 (VSS), RAM.30 (A17)
INST0: INST.2 (O0)
INST1: INST.5 (O1)
INST2: INST.6 (O2)
INST3: INST.9 (O3)
INST4: INST.12 (O4)
INST5: INST.15 (O5)
INST6: INST.16 (O6)
INST7: INST.19 (O7)
INST_s: INST.11 (LE)
unnamed: CTRL.4, CTRL_AND.3
unnamed: CTRL.6, CTRL.9
unnamed: CTRL.8, CTRL.12
~ADDRH_e: ADDRH_OUT.1 (1OE), ADDRH_OUT.19 (2OE)
~ADDRL_e: ADDRL_OUT.1 (1OE), ADDRL_OUT.19 (2OE)
~RAM_e: RAM.24 (OE#)
~RAM_s: RAM.29 (WE#)

Notes on the sheet:
RAM chip will be enabled when addr < 0xFF80
