patrickleboutillier/flash6502/docs/kicad/flash6502/Registers.kicad_sch

## KiCad design docs/kicad/flash6502/Registers.kicad_sch (2023-03-12, an earlier design)

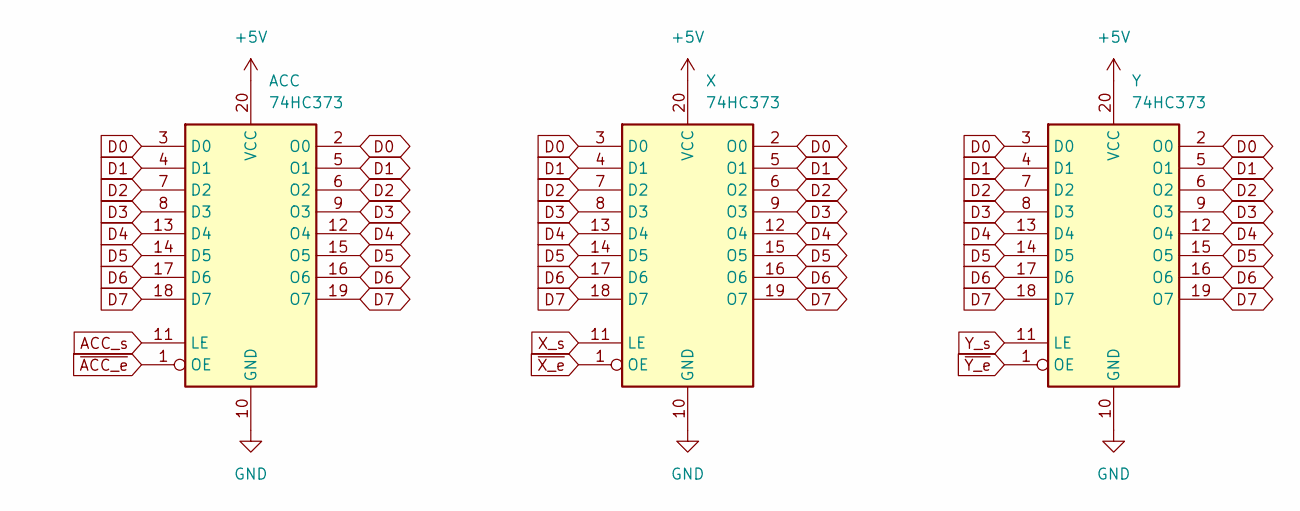
[picture p32: schematic Registers.kicad_sch]

Parts:
ACC: 74HC373
X: 74HC373
Y: 74HC373

Connections:
+5V: ACC.20 (VCC), X.20 (VCC), Y.20 (VCC)
ACC_s: ACC.11 (LE)
D0: ACC.2 (O0), ACC.3 (D0), X.2 (O0), X.3 (D0), Y.2 (O0), Y.3 (D0)
D1: ACC.4 (D1), ACC.5 (O1), X.4 (D1), X.5 (O1), Y.4 (D1), Y.5 (O1)
D2: ACC.6 (O2), ACC.7 (D2), X.6 (O2), X.7 (D2), Y.6 (O2), Y.7 (D2)
D3: ACC.8 (D3), ACC.9 (O3), X.8 (D3), X.9 (O3), Y.8 (D3), Y.9 (O3)
D4: ACC.12 (O4), ACC.13 (D4), X.12 (O4), X.13 (D4), Y.12 (O4), Y.13 (D4)
D5: ACC.14 (D5), ACC.15 (O5), X.14 (D5), X.15 (O5), Y.14 (D5), Y.15 (O5)
D6: ACC.16 (O6), ACC.17 (D6), X.16 (O6), X.17 (D6), Y.16 (O6), Y.17 (D6)
D7: ACC.18 (D7), ACC.19 (O7), X.18 (D7), X.19 (O7), Y.18 (D7), Y.19 (O7)
GND: ACC.10 (GND), X.10 (GND), Y.10 (GND)
X_s: X.11 (LE)
Y_s: Y.11 (LE)
~ACC_e: ACC.1 (OE)
~X_e: X.1 (OE)
~Y_e: Y.1 (OE)
