patrickleboutillier/flash6502/docs/kicad/flash6502/Status.kicad_sch

## KiCad design docs/kicad/flash6502/Status.kicad_sch (2023-03-12, an earlier design)

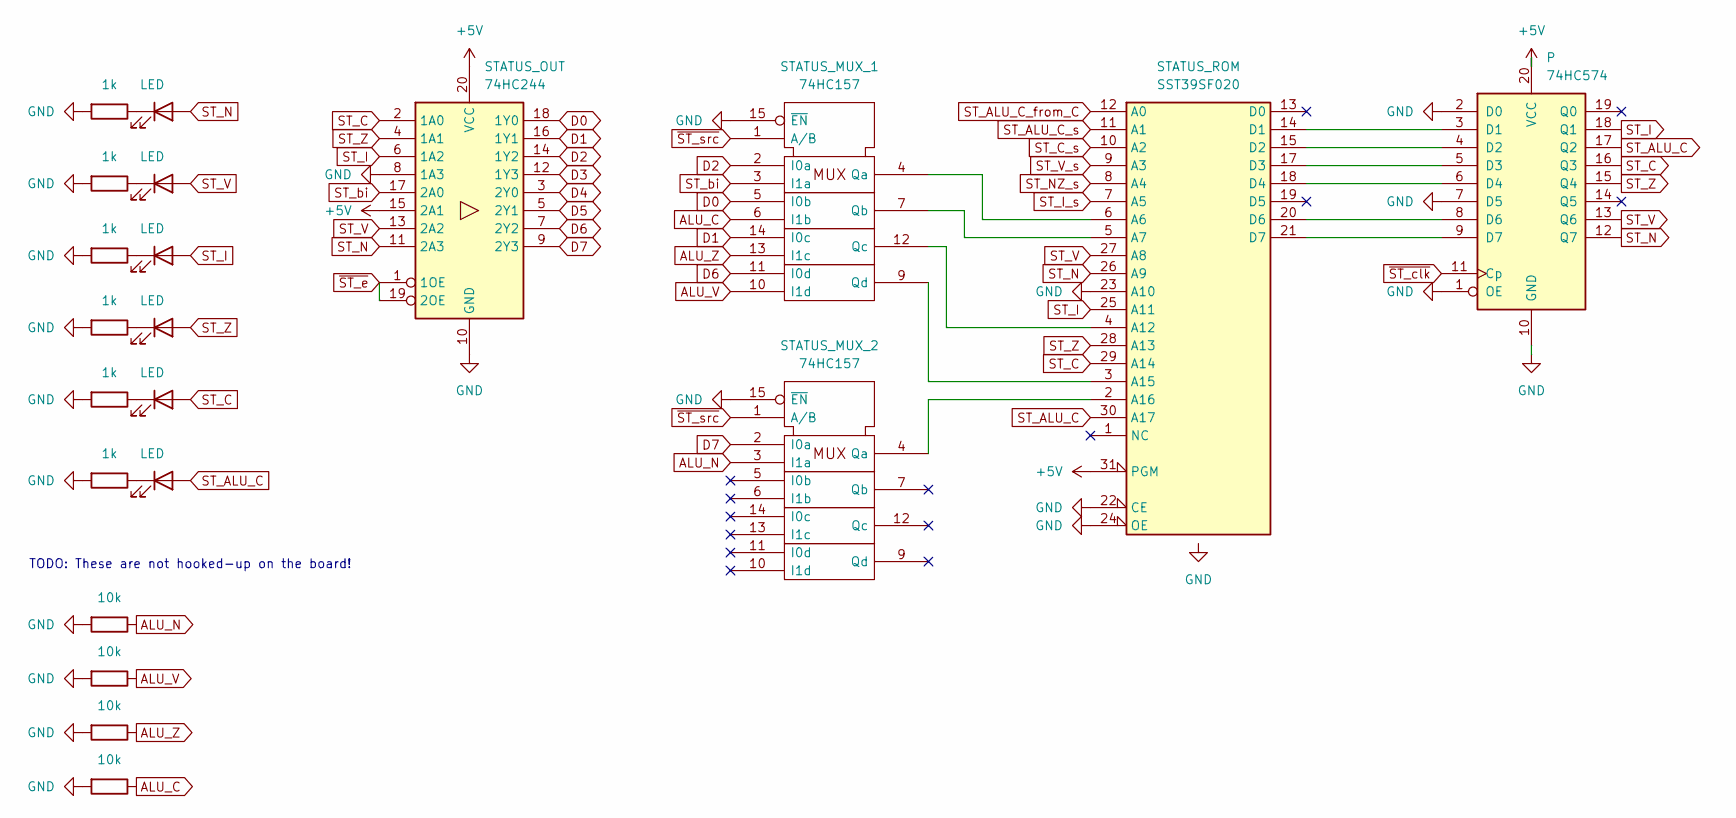
[picture p33: schematic Status.kicad_sch]

Parts:
LEDALUC: LED
LEDC: LED
LEDI: LED
LEDN: LED
LEDV: LED
LEDZ: LED
P: 74HC574
RALUC: 10k
RALUN: 10k
RALUV: 10k
RALUZ: 10k
RC: 1k
RI: 1k
RN: 1k
RSTALUC: 1k
RV: 1k
RZ: 1k
STATUS_MUX_1, STATUS_MUX_2: 74HC157
STATUS_OUT: 74HC244
STATUS_ROM: SST39SF020

Connections:
+5V: P.20 (VCC), STATUS_OUT.15 (2A1), STATUS_OUT.20 (VCC), STATUS_ROM.31 (PGM)
ALU_C: RALUC.1, STATUS_MUX_1.6 (I1b)
ALU_N: RALUN.1, STATUS_MUX_2.3 (I1a)
ALU_V: RALUV.1, STATUS_MUX_1.10 (I1d)
ALU_Z: RALUZ.1, STATUS_MUX_1.13 (I1c)
D0: STATUS_MUX_1.5 (I0b), STATUS_OUT.18 (1Y0)
D1: STATUS_MUX_1.14 (I0c), STATUS_OUT.16 (1Y1)
D2: STATUS_MUX_1.2 (I0a), STATUS_OUT.14 (1Y2)
D3: STATUS_OUT.12 (1Y3)
D4: STATUS_OUT.3 (2Y0)
D5: STATUS_OUT.5 (2Y1)
D6: STATUS_MUX_1.11 (I0d), STATUS_OUT.7 (2Y2)
D7: STATUS_MUX_2.2 (I0a), STATUS_OUT.9 (2Y3)
GND: P.1 (OE), P.2 (D0), P.7 (D5), P.10 (GND), RALUC.2, RALUN.2, RALUV.2, RALUZ.2, RC.2, RI.2, RN.2, RSTALUC.2, RV.2, RZ.2, STATUS_MUX_1.15 (~EN), STATUS_MUX_2.15 (~EN), STATUS_OUT.8 (1A3), STATUS_OUT.10 (GND), STATUS_ROM.16 (GND), STATUS_ROM.22 (CE), STATUS_ROM.23 (A10), STATUS_ROM.24 (OE)
unnamed: LEDALUC.1 (K), RSTALUC.1
unnamed: LEDC.1 (K), RC.1
unnamed: LEDI.1 (K), RI.1
unnamed: LEDN.1 (K), RN.1
unnamed: LEDV.1 (K), RV.1
unnamed: LEDZ.1 (K), RZ.1
unnamed: P.3 (D1), STATUS_ROM.14 (D1)
unnamed: P.4 (D2), STATUS_ROM.15 (D2)
unnamed: P.5 (D3), STATUS_ROM.17 (D3)
unnamed: P.6 (D4), STATUS_ROM.18 (D4)
unnamed: P.8 (D6), STATUS_ROM.20 (D6)
unnamed: P.9 (D7), STATUS_ROM.21 (D7)
unnamed: STATUS_MUX_1.4 (Qa), STATUS_ROM.6 (A6)
unnamed: STATUS_MUX_1.7 (Qb), STATUS_ROM.5 (A7)
unnamed: STATUS_MUX_1.9 (Qd), STATUS_ROM.3 (A15)
unnamed: STATUS_MUX_1.12 (Qc), STATUS_ROM.4 (A12)
unnamed: STATUS_MUX_2.4 (Qa), STATUS_ROM.2 (A16)
ST_ALU_C: LEDALUC.2 (A), P.17 (Q2), STATUS_ROM.30 (A17)
ST_ALU_C_from_C: STATUS_ROM.12 (A0)
ST_ALU_C_s: STATUS_ROM.11 (A1)
ST_C: LEDC.2 (A), P.16 (Q3), STATUS_OUT.2 (1A0), STATUS_ROM.29 (A14)
ST_C_s: STATUS_ROM.10 (A2)
ST_I: LEDI.2 (A), P.18 (Q1), STATUS_OUT.6 (1A2), STATUS_ROM.25 (A11)
ST_I_s: STATUS_ROM.7 (A5)
ST_N: LEDN.2 (A), P.12 (Q7), STATUS_OUT.11 (2A3), STATUS_ROM.26 (A9)
ST_NZ_s: STATUS_ROM.8 (A4)
ST_V: LEDV.2 (A), P.13 (Q6), STATUS_OUT.13 (2A2), STATUS_ROM.27 (A8)
ST_V_s: STATUS_ROM.9 (A3)
ST_Z: LEDZ.2 (A), P.15 (Q4), STATUS_OUT.4 (1A1), STATUS_ROM.28 (A13)
ST_bi: STATUS_MUX_1.3 (I1a), STATUS_OUT.17 (2A0)
~ST_clk: P.11 (Cp)
~ST_e: STATUS_OUT.1 (1OE), STATUS_OUT.19 (2OE)
~ST_src: STATUS_MUX_1.1 (A/B), STATUS_MUX_2.1 (A/B)

Notes on the sheet:
TODO: These are not hooked-up on the board!
