patrickleboutillier/flash6502/docs/kicad/flash6502/flash6502.kicad_sch

## KiCad design docs/kicad/flash6502/flash6502.kicad_sch (2023-03-12, an earlier design)

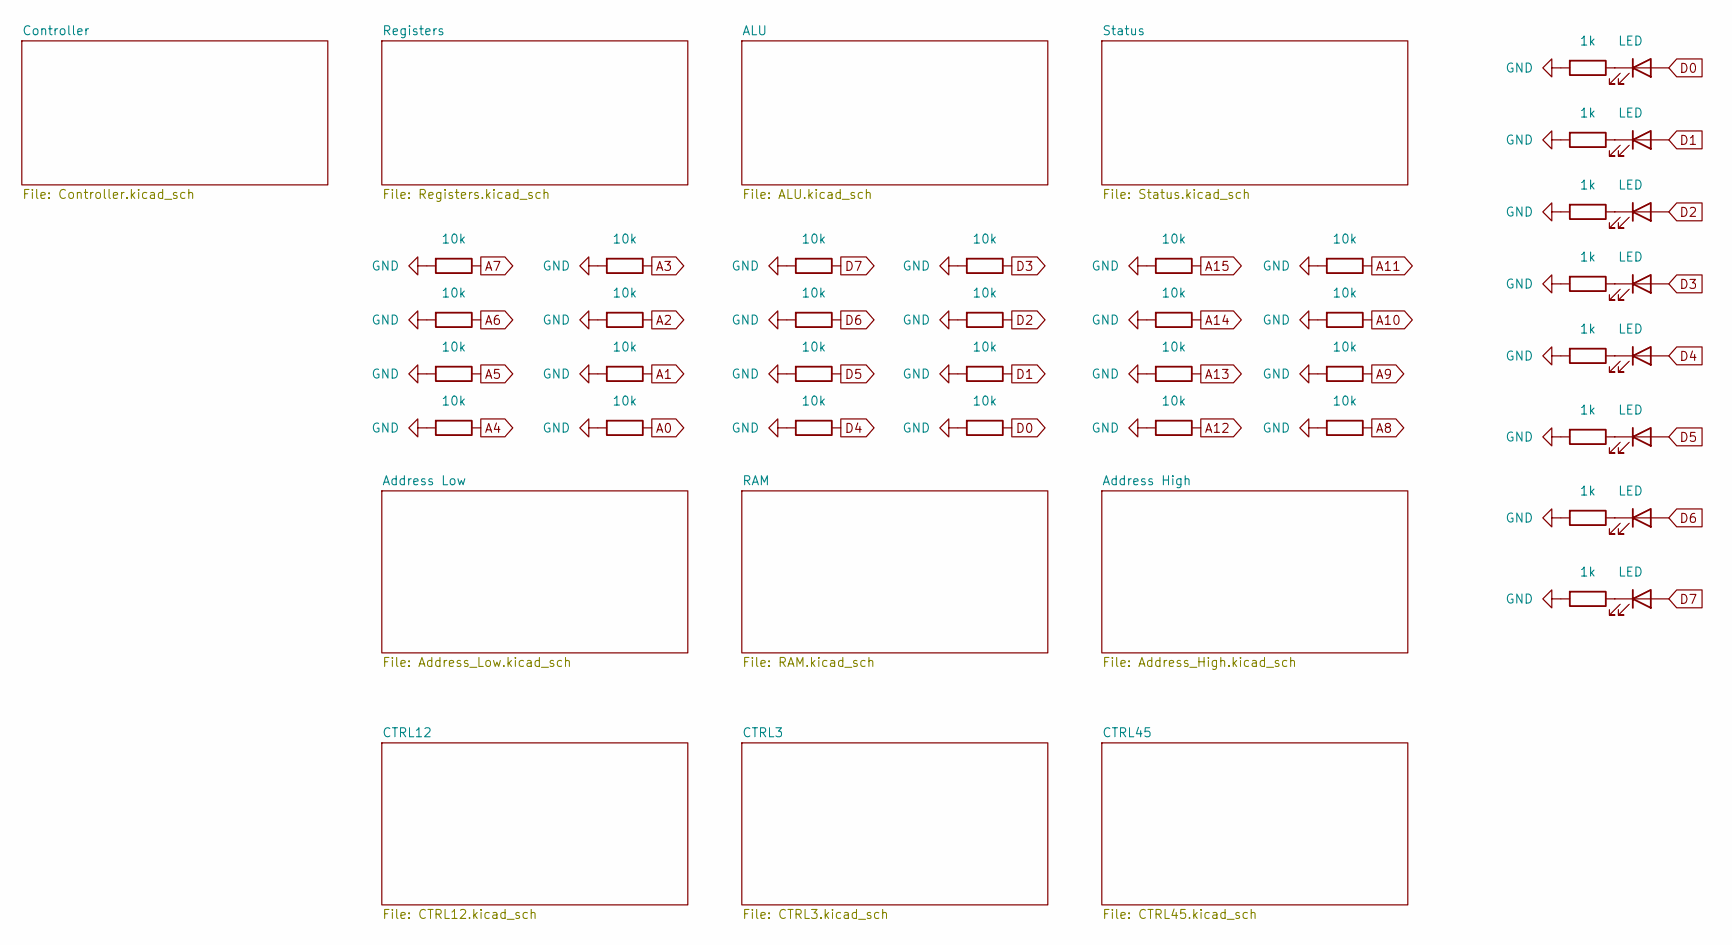
[picture p34: schematic flash6502.kicad_sch]

Parts:
LEDD0, LEDD1, LEDD2, LEDD3, LEDD4, LEDD5, LEDD6, LEDD7: LED
RA0, RA1, RA2, RA3, RA4, RA5, RA6, RA7, RA8, RA9, RA10, RA11, RA12, RA13, RA14, RA15: 10k
RD0, RD1, RD3, RD4, RD5, RD6, RD7: 10k
RLD0, RLD1, RLD2, RLD3, RLD4, RLD5, RLD6, RLD7: 1k
RRD2: 10k

Connections:
A0: RA0.1
A1: RA1.1
A2: RA2.1
A3: RA3.1
A4: RA4.1
A5: RA5.1
A6: RA6.1
A7: RA7.1
A8: RA8.1
A9: RA9.1
A10: RA10.1
A11: RA11.1
A12: RA12.1
A13: RA13.1
A14: RA14.1
A15: RA15.1
D0: LEDD0.2 (A), RD0.1
D1: LEDD1.2 (A), RD1.1
D2: LEDD2.2 (A), RRD2.1
D3: LEDD3.2 (A), RD3.1
D4: LEDD4.2 (A), RD4.1
D5: LEDD5.2 (A), RD5.1
D6: LEDD6.2 (A), RD6.1
D7: LEDD7.2 (A), RD7.1
GND: RA0.2, RA1.2, RA2.2, RA3.2, RA4.2, RA5.2, RA6.2, RA7.2, RA8.2, RA9.2, RA10.2, RA11.2, RA12.2, RA13.2, RA14.2, RA15.2, RD0.2, RD1.2, RD3.2, RD4.2, RD5.2, RD6.2, RD7.2, RLD0.2, RLD1.2, RLD2.2, RLD3.2, RLD4.2, RLD5.2, RLD6.2, RLD7.2, RRD2.2
unnamed: LEDD0.1 (K), RLD0.1
unnamed: LEDD1.1 (K), RLD1.1
unnamed: LEDD2.1 (K), RLD2.1
unnamed: LEDD3.1 (K), RLD3.1
unnamed: LEDD4.1 (K), RLD4.1
unnamed: LEDD5.1 (K), RLD5.1
unnamed: LEDD6.1 (K), RLD6.1
unnamed: LEDD7.1 (K), RLD7.1
