patrickleboutillier/flash6502/arduino/flash6502/TEST.h

PROGMEM const uint8_t test_suite[] = {
  /* PC:0x0000 */  0x4C,  0x00,  0x04,  0x00,  0x00,  0x00,  0x00,  0x00,  0x00,  0x00,  0x00,  0x00,  0x00,  0x00,  0x00,  0x00,
  /* PC:0x0010 */  0x00,  0x00,  0x00,  0x80,  0x01,  0xC3,  0x82,  0x41,  0x00,  0x7F,  0x00,  0x1F,  0x71,  0x80,  0x0F,  0xFF,
  /* PC:0x0020 */  0x7F,  0x80,  0xFF,  0x0F,  0x8F,  0x8F,  0x18,  0x02,  0x19,  0x02,  0x1A,  0x02,  0x1B,  0x02,  0x1C,  0x02,
  /* PC:0x0030 */  0x20,  0x01,  0x03,  0x02,  0x04,  0x02,  0x05,  0x02,  0x06,  0x02,  0x0B,  0x01,  0x5F,  0x02,  0x60,  0x02,
  /* PC:0x0040 */  0x61,  0x02,  0x62,  0x02,  0x63,  0x02,  0x64,  0x02,  0x65,  0x02,  0x66,  0x02,  0x5B,  0x02,  0x5C,  0x02,
  /* PC:0x0050 */  0x5D,  0x02,  0x5E,  0x02,  0x03,  0x02,  0x04,  0x02,  0x04,  0x01,  0x05,  0x01,  0xFF,  0xFF,  0xFF,  0xFF,
  /* PC:0x0060 */  0xFF,  0xFF,  0xFF,  0xFF,  0xFF,  0xFF,  0xFF,  0xFF,  0xFF,  0xFF,  0xFF,  0xFF,  0xFF,  0xFF,  0xFF,  0xFF,
  /* PC:0x0070 */  0xFF,  0xFF,  0xFF,  0xFF,  0xFF,  0xFF,  0xFF,  0xFF,  0xFF,  0xFF,  0xFF,  0xFF,  0xFF,  0xFF,  0xFF,  0xFF,
  /* PC:0x0080 */  0xFF,  0xFF,  0xFF,  0xFF,  0xFF,  0xFF,  0xFF,  0xFF,  0xFF,  0xFF,  0xFF,  0xFF,  0xFF,  0xFF,  0xFF,  0xFF,
  /* PC:0x0090 */  0xFF,  0xFF,  0xFF,  0xFF,  0xFF,  0xFF,  0xFF,  0xFF,  0xFF,  0xFF,  0xFF,  0xFF,  0xFF,  0xFF,  0xFF,  0xFF,
  /* PC:0x00A0 */  0xFF,  0xFF,  0xFF,  0xFF,  0xFF,  0xFF,  0xFF,  0xFF,  0xFF,  0xFF,  0xFF,  0xFF,  0xFF,  0xFF,  0xFF,  0xFF,
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
  /* PC:0x3920 */  0xAD,  0xFE,  0x01,  0xC9,  0x1D,  0xD0,  0xFE,  0xA9,  0x04,  0x48,  0xA6,  0x0B,  0xE8,  0xA5,  0x0A,  0x49,
  /* PC:0x3930 */  0xAA,  0x28,  0x40,  0x4C,  0x33,  0x39,  0x4C,  0x00,  0x04
} ;
